KargJonas/project-zedekiel/case/drafts/foot.jpg

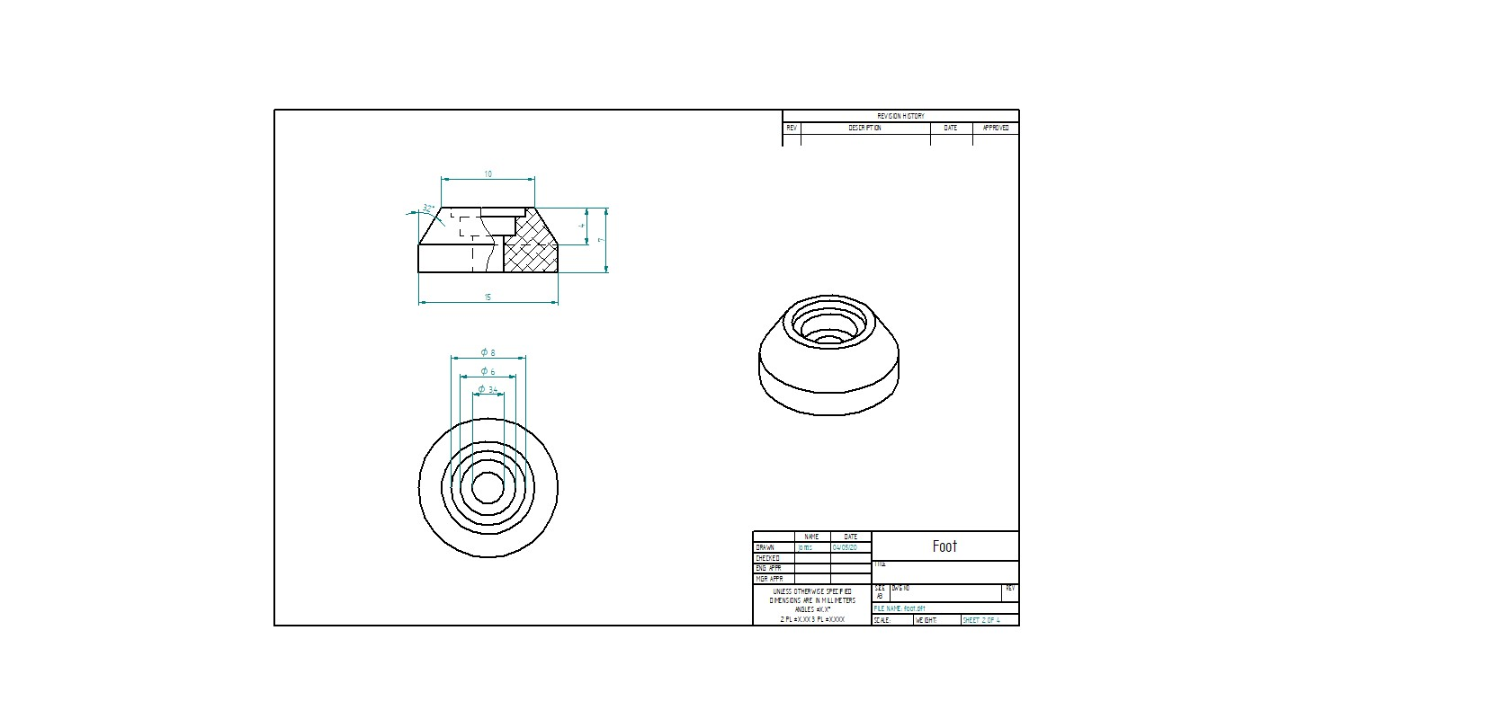
case/drafts/foot.jpg
