KargJonas/project-zedekiel/misc/images/doom-converted.png

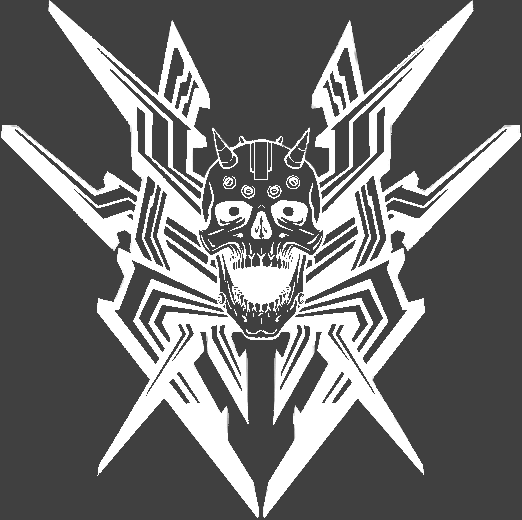
misc/images/doom-converted.png
