KargJonas/project-zedekiel/misc/images/doom.png

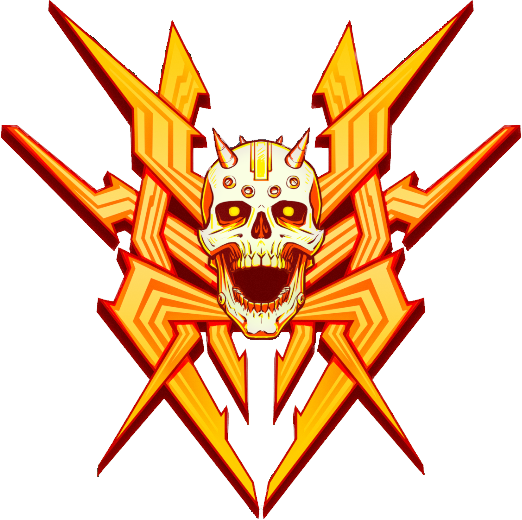
misc/images/doom.png
