KargJonas/project-zedekiel/misc/images/prototype/edge.jpg

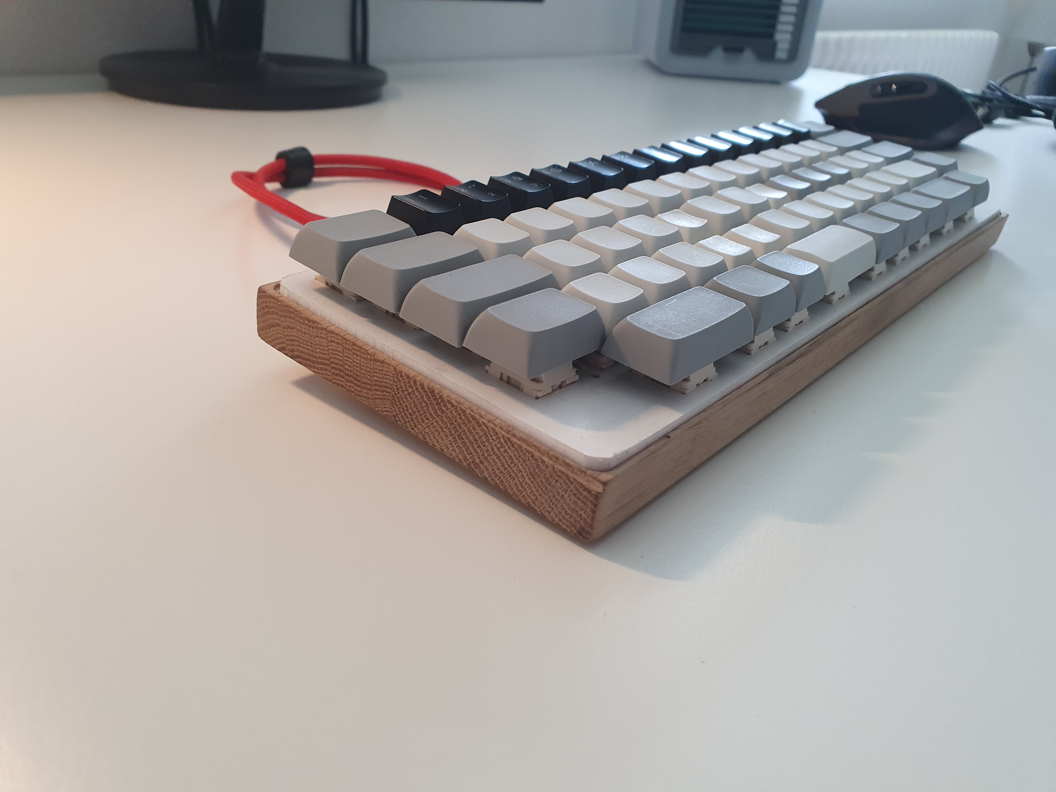
misc/images/prototype/edge.jpg
