KargJonas/project-zedekiel/misc/images/silk-art-polygons.png

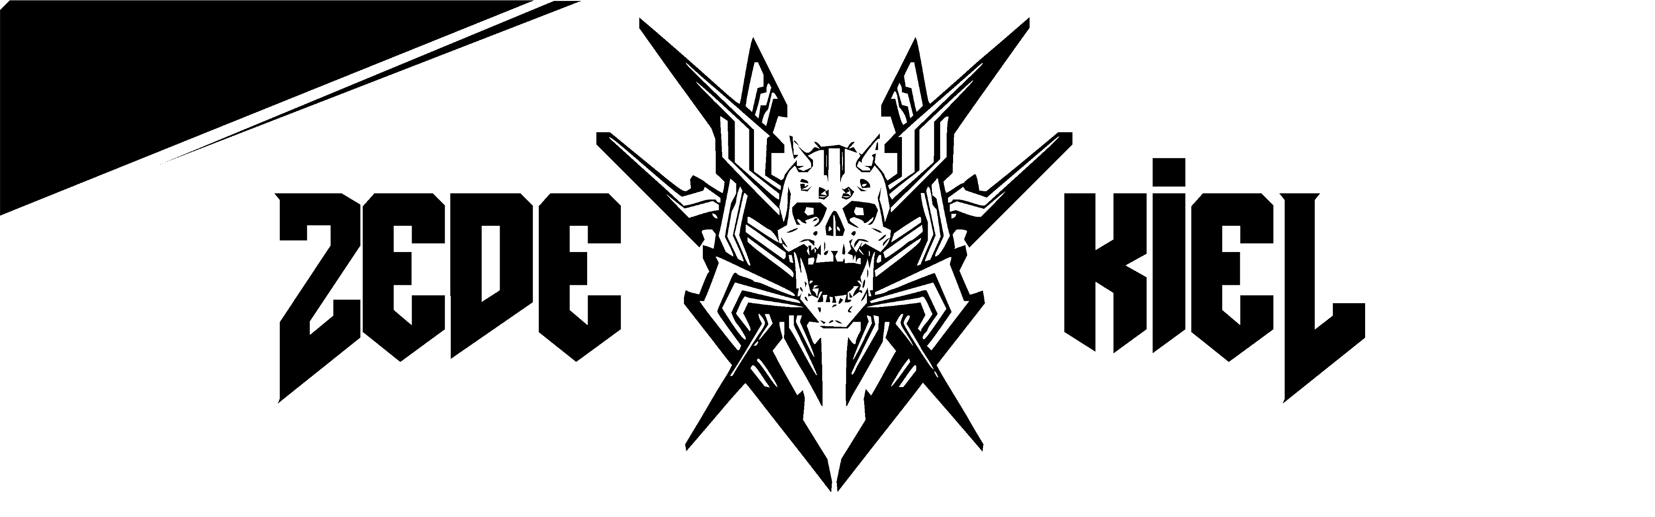
misc/images/silk-art-polygons.png
