KargJonas/project-zedekiel/misc/resources/switch-dimensions-2.jpg

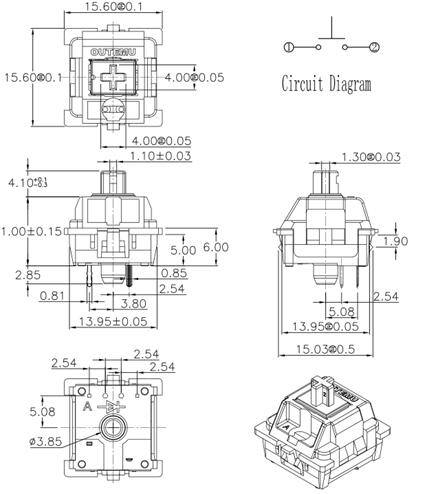
misc/resources/switch-dimensions-2.jpg
