KargJonas/project-zedekiel/renders/pcb-v0.2-4.png

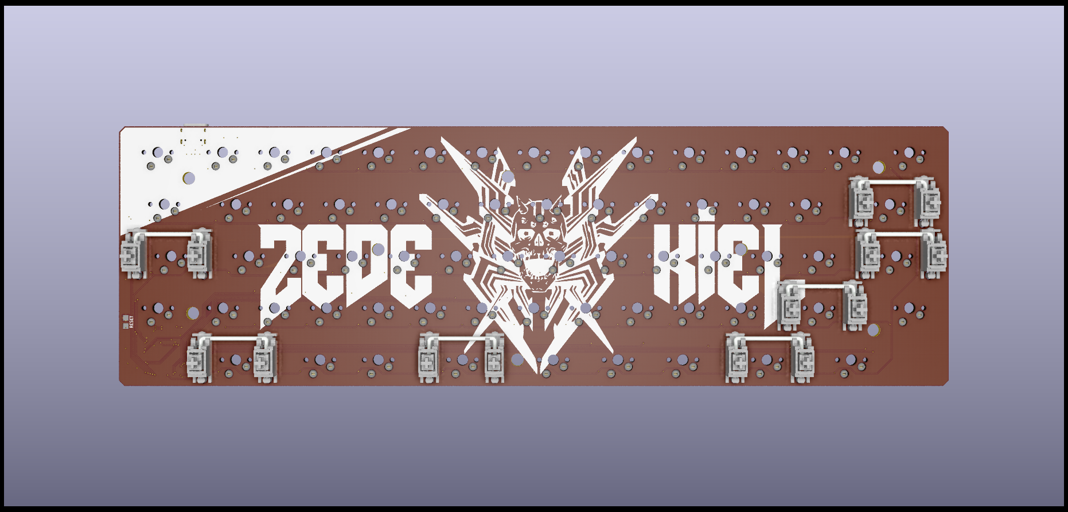
renders/pcb-v0.2-4.png
