KargJonas/project-zedekiel/renders/pcb-v0.2-8.png

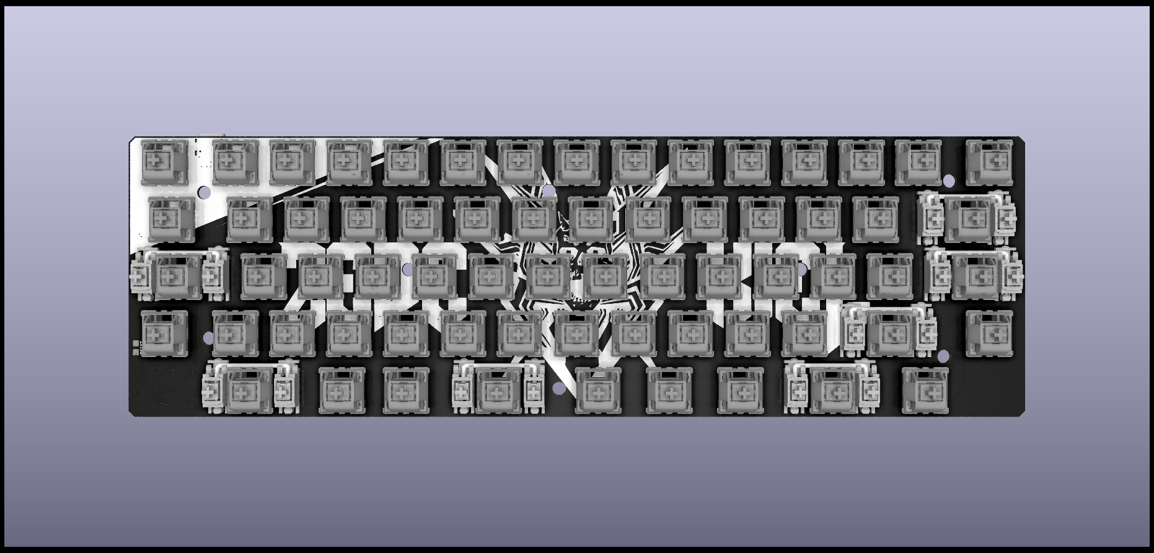
renders/pcb-v0.2-8.png
