KargJonas/project-zedekiel/renders/pcb.png

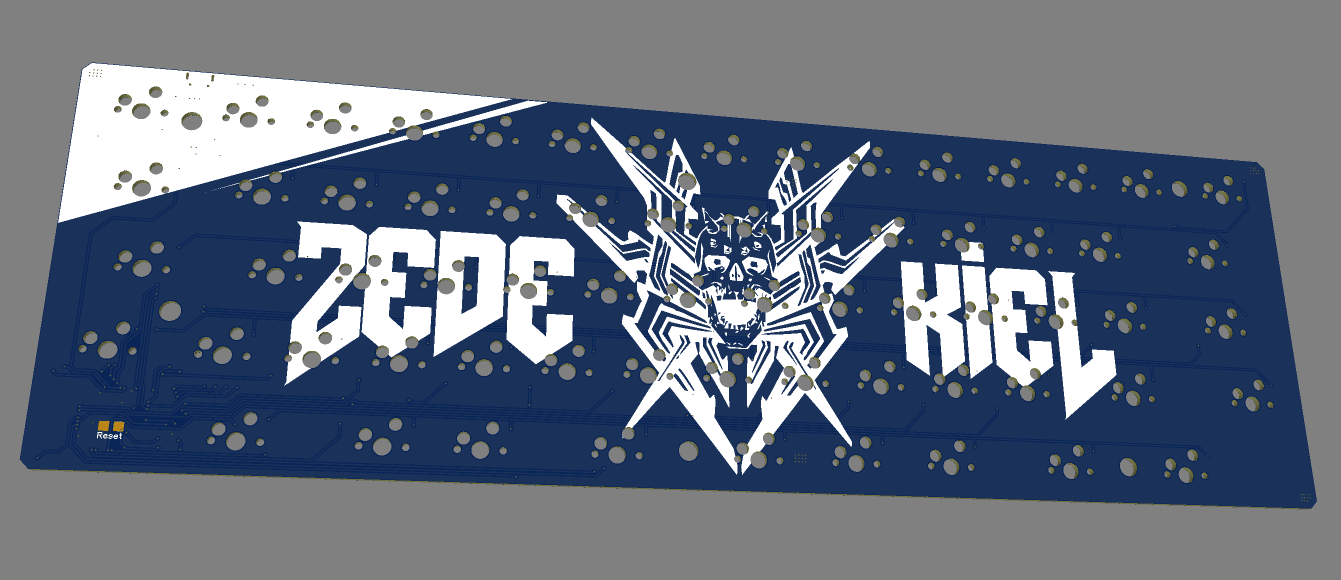
renders/pcb.png
