KargJonas/project-zedekiel/renders/assembled.jpg

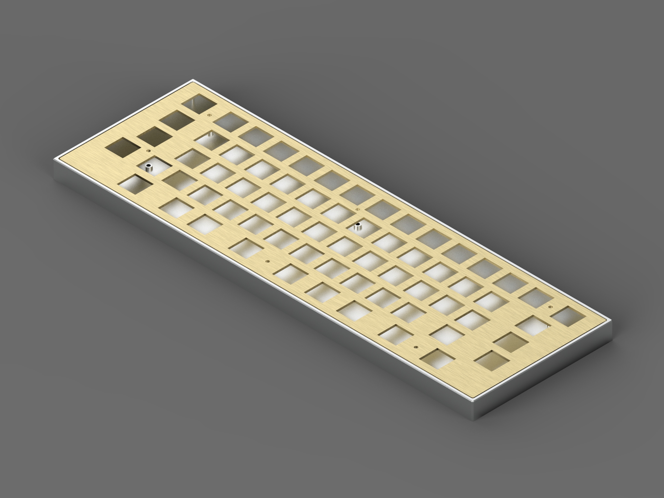
renders/assembled.jpg
