KargJonas/project-zedekiel/renders/assembly-v0.2-1.png

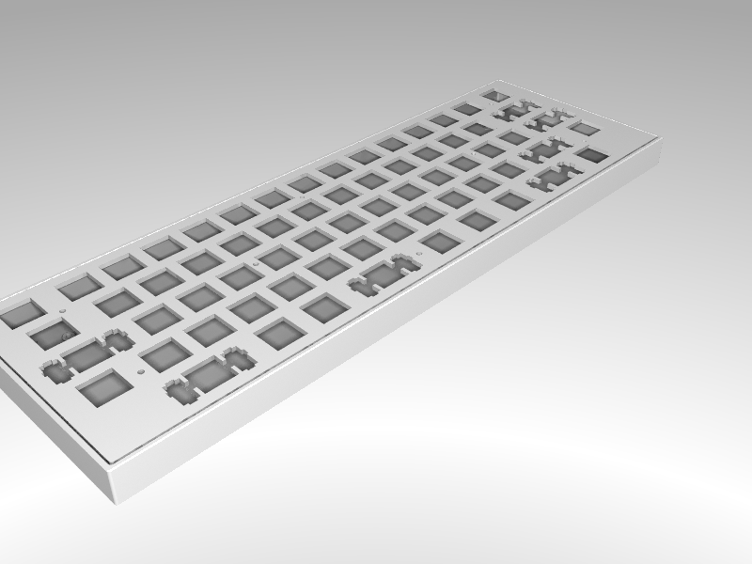
renders/assembly-v0.2-1.png
